erebusnz/tachyon/gerber/audit-backing-board.md

# PCB Audit — backing-board

**Auto-generated by `.claude/skills/pcb-designer/scripts/run_audit.py`**

## Sources

- Telesis netlist: indexed (31 package types, 59 nets)
- Pick-and-place: 74 components
- Gerber: gerber\audio-mcu-board (16 layers)

## Findings

- Layout errors (need EasyEDA Pro fix): **0**
- Stale documentation (need MD edit): **0**
- Advisories: **0**

## Observations

- Stackup: 4-layer (15 gerber layers). G1 (regions=251, copper_areas=0). G2 (regions=6, copper_areas=6).
- .G1: single GND pour ✓ (regions=251, copper_areas=0). Confirm electrical continuity visually if encoded as many SolidRegions.
- .G2: 6 PlaneZones — power layer split per pcb-design.md §4 ✓ (matches expected rail count)
- Board outline: 48.00 × 110.00 mm (X[0.00,48.00] Y[-110.00,0.00])
- Named nets: ['+12V', '+3V3', '+3V3_AUDIO', '+3V3_PREC', '+5V', '-12V', '-12VEURO', '12VEURO', 'A-OUT-L', 'A-OUT-R', 'CLK-IN', 'CV-IN-A', 'CV-IN-B', 'CV-OUT-A', 'CV-OUT-B', 'DAC-SPI-CS', 'DAC-SPI-MOSI', 'DAC-SPI-SCLK', 'GATE-OUT-A', 'GATE-OUT-B', 'GND', 'I2S3_BCK', 'I2S3_SD', 'I2S3_WS', 'U12-BOOT', 'U12-FB', 'U12-SW', 'USR-ENC-A', 'USR-ENC-B', 'USR-ENC-SW', 'USR-POT-1', 'VREF', '~MUTE']
- Anonymous (auto-generated $...) nets: 21
- Single ground net (GND): ✓ matches pcb-design.md §3.
- Datasheet power/ground pin connectivity: 17 power/GND pin(s) across 5 IC(s) all connected ✓ (would flag a floating supply/GND pin, e.g. the U6 pin-8 GND case).
- Eurorack 10-pin header P1: standard pinout ✓ ({-12V:[1, 2], GND:[3, 4, 5, 6, 7, 8], +12V:[9, 10]}). Verify silk stripe sits on -12V edge in EasyEDA Pro 2D view.
- Pass 3: skipping U1 (sub-module with internal decoupling).
- Decoupling U12 +12V: nearest cap C5 at 3.05 mm ✓
- Decoupling U14 +3V3_PREC: nearest cap C11 at 3.79 mm ✓
- Decoupling U14 +5V: nearest cap C9 at 4.75 mm ✓
- Decoupling U15 +3V3_AUDIO: nearest cap C14 at 3.84 mm ✓
- Decoupling U15 +5V: nearest cap C12 at 5.04 mm ✓
- Decoupling U16 +12V: nearest cap C36 at 6.04 mm ✓
- Decoupling U16 -12V: nearest cap C35 at 5.23 mm ✓
- Decoupling U2 +3V3_PREC: nearest cap C15 at 5.39 mm ✓
- Decoupling U3 +3V3: nearest cap C26 at 6.65 mm ✓
- Decoupling U3 +3V3_AUDIO: nearest cap C31 at 5.80 mm ✓
- Decoupling U6 +3V3_PREC: nearest cap C18 at 5.38 mm ✓
- Decoupling U7 +12V: nearest cap C22 at 5.49 mm ✓
- Decoupling U7 -12V: nearest cap C23 at 5.43 mm ✓
- Spacing U12↔U3 = 50.40 mm (ge 30.0 mm): ✓ — TPS54202 (noisy buck) ↔ PCM5102A (audio DAC) — pcb-design.md §5
- Spacing U12↔U2 = 44.30 mm (ge 30.0 mm): ✓ — TPS54202 (noisy buck) ↔ REF5025 (precision ref) — pcb-design.md §5
- Spacing U12↔U16 = 33.53 mm (ge 30.0 mm): ✓ — TPS54202 (noisy buck) ↔ OPA1642 audio buffers — analogous to U3
- Spacing U2↔U6 = 11.65 mm (le 20.0 mm): ✓ — REF5025 ↔ DAC8552 — cv-output-dac.md §6 (VREF trace)
- Placement U12  at (   7.6,    -5.6) side=top    fp=SOT-23-6_L2.9-W1.6-P0.95-LS2.8-BL
- Placement P1   at (  41.9,   -11.6) side=bottom fp=IDC-TH_10P-P2.54_C5665
- Placement U14  at (  28.8,   -31.0) side=top    fp=SOT-23-5_L2.9-W1.6-P0.95-LS2.8-BR
- Placement U15  at (  17.5,   -30.9) side=top    fp=SOT-23-5_L2.9-W1.6-P0.95-LS2.8-BR
- Placement U16  at (   8.1,   -39.1) side=top    fp=SOIC-8_L4.9-W3.9-P1.27-LS6.0-BL
- Placement U2   at (  27.9,   -45.0) side=top    fp=SOIC-8_L4.9-W3.9-P1.27-LS6.0-BL-4
- Placement U7   at (  37.6,   -44.2) side=top    fp=SOIC-8_L4.9-W3.9-P1.27-LS6.0-BL
- Placement U6   at (  31.2,   -56.1) side=top    fp=VSSOP-8_L3.0-W3.0-P0.65-LS5.0-BL
- Placement U3   at (  15.5,   -55.4) side=top    fp=TSSOP-20_L6.5-W4.4-P0.65-LS6.4-BL
- Placement U1   at (  24.5,   -81.8) side=bottom fp=WeAct STM32F405RGT6
- Placement H2   at (   3.0,   -39.6) side=top    fp=HDR-TH_4P-P2.54-V-M-1
- Placement H3   at (  45.0,   -32.3) side=top    fp=HDR-TH_8P-P2.54-V-M
- Placement H4   at (   3.0,   -72.6) side=top    fp=HDR-TH_8P-P2.54-V-M
- Placement H9   at (  45.0,   -77.7) side=top    fp=HDR-TH_12P-P2.54-V-M
- I2S3_BCK: members ['U1', 'U3']
- I2S3_SD: members ['U1', 'U3']
- I2S3_WS: members ['U1', 'U3']
- Trace widths on .GBL: 0.203mm×476, 0.254mm×63, 0.500mm×11, 1.000mm×13
- Trace widths on .G2: 0.203mm×670
- Trace widths on .GTL: 0.203mm×1349, 0.254mm×281, 0.400mm×9, 0.500mm×41, 0.700mm×4, 0.750mm×1, 0.800mm×2, 1.000mm×32
- Per-net trace-width compliance (e.g. '+5V must be ≥ 0.6 mm') cannot be verified from gerber geometry alone — the gerber encodes geometry without net assignment. Verify visually in the EasyEDA Pro 2D view or by exporting routed length per net from the project.
