erebusnz/tachyon/gerber/audit-front-board.md

# PCB Audit — front-board

**Auto-generated by `.claude/skills/pcb-designer/scripts/run_audit.py`**

## Sources

- Telesis netlist: indexed (0 package types, 0 nets)
- Pick-and-place: 8 components
- Gerber: gerber\front-board (9 layers)

## Findings

- Layout errors (need EasyEDA Pro fix): **0**
- Stale documentation (need MD edit): **0**
- Advisories: **0**

## Observations

- Stackup: 2-layer (9 gerber layers, no .G1/.G2)
- Board outline: 50.50 × 128.50 mm (X[-26.05,24.45] Y[-64.16,64.34])

## Skipped passes

- Passes 2-6: no electrical content (empty netlist)
