erebusnz/tachyon/gerber/audit-io-board.md

# PCB Audit — io-board

**Auto-generated by `.claude/skills/pcb-designer/scripts/run_audit.py`**

## Sources

- Telesis netlist: indexed (15 package types, 37 nets)
- Pick-and-place: 44 components
- Gerber: gerber\io-board (16 layers)

## Findings

- Layout errors (need EasyEDA Pro fix): **0**
- Stale documentation (need MD edit): **0**
- Advisories: **0**

## Observations

- Stackup: 4-layer (15 gerber layers). G1 (regions=212, copper_areas=0). G2 (regions=212, copper_areas=0).
- .G1: single GND pour ✓ (regions=212, copper_areas=0). Confirm electrical continuity visually if encoded as many SolidRegions.
- .G2: single GND pour ✓ (regions=212, copper_areas=0). Confirm electrical continuity visually if encoded as many SolidRegions.
- Board outline: 49.27 × 119.53 mm (X[0.00,49.27] Y[-119.53,0.00])
- Named nets: ['+12V', '+3V3', '+5V', '-12V', 'A-OUT-L', 'A-OUT-R', 'CLK-IN', 'CV-IN-A', 'CV-IN-B', 'CV-OUT-A', 'CV-OUT-B', 'GATE-OUT-A', 'GATE-OUT-B', 'GND', 'USR-ENC-A', 'USR-ENC-B', 'USR-ENC-SW', 'USR-POT-1', 'VREF']
- Anonymous (auto-generated $...) nets: 18
- Single ground net (GND): ✓ matches pcb-design.md §3.
- Decoupling U23 +12V: nearest cap C40 at 5.23 mm ✓
- Decoupling U23 -12V: nearest cap C41 at 5.57 mm ✓
- Pass 4: no spacing rules defined for io-board in SPACING_RULES.
- Trace widths on .GBL: 0.203mm×712, 0.254mm×234, 0.500mm×9
- Trace widths on .GTL: 0.203mm×789, 0.254mm×247
- Per-net trace-width compliance (e.g. '+5V must be ≥ 0.6 mm') cannot be verified from gerber geometry alone — the gerber encodes geometry without net assignment. Verify visually in the EasyEDA Pro 2D view or by exporting routed length per net from the project.

## Skipped passes

- Pass 5 (I2S): no I2S on this board.
