erebusnz/tachyon/datasheets/REF5025.md

# REF5025 -- Low-Noise, Very Low Drift, 2.5V Precision Voltage Reference

## BOM Details

| Field | Value |
|---|---|
| MPN | REF5025IDR |
| Manufacturer | TI |
| Package | SOIC-8_L4.9-W3.9-P1.27-LS6.0-BL-4 |
| Designator | U2 |
| Quantity | 1 |
| Supplier Part  | C544535 (LCSC) |

## Description

The REF5025 is a low-noise, low-drift, precision 2.5V voltage reference from the REF50xx family by Texas Instruments. The standard-grade REF5025IDR (I-suffix) provides 0.1% initial accuracy (max) and 8 ppm/degC temperature drift (max). The higher-grade REF5025AIDR (AI-suffix) tightens these to 0.05% and 3 ppm/degC. It is capable of sourcing and sinking up to 10 mA of output current, making it suitable for driving ADC and DAC reference inputs.

## Key Electrical Characteristics

All values at TA = 25 degC, ILOAD = 0, CL = 1 uF, VIN = (VOUT + 0.2V) to 18V unless otherwise noted. REF5025IDR is the standard-grade (I-suffix) device.

| Parameter | Min | Typ | Max | Unit | Condition |
|---|---|---|---|---|---|
| Output voltage | 2.4975 | 2.5000 | 2.5025 | V | TA = 25 degC, derived from ±0.1 % accuracy |
| Initial accuracy (standard grade) | -0.1 | | +0.1 | % | All voltage options, TA = 25 degC |
| Temperature drift (standard grade) | | 3 | 8 | ppm/degC| TA = -40 degC to +125 degC |
| Low-frequency noise | | 3 | | uVpp/V  | f = 0.1 Hz to 10 Hz (= 7.5 uVpp at 2.5 V) |
| Output voltage noise | | 0.9 | | uVrms/V | f = 10 Hz to 1 kHz, integrated |
| Line regulation | | 1 | 3 | ppm/V | VIN = (VOUT + 0.2V) to 18V |
| Line regulation (over temperature) | | 1 | 5 | ppm/V | VIN = (VOUT + 0.2V) to 18V, -40 to +125 degC |
| Load regulation | | 20 | 30 | ppm/mA  | -10 mA < IOUT < 10 mA, VIN = VOUT + 0.75V |
| Load regulation (over temperature) | | | 50 | ppm/mA  | -10 mA < IOUT < 10 mA, -40 to +125 degC |
| Short-circuit current | | 25 | | mA | VOUT shorted to GND |
| Output current (source/sink) | -10 | | +10 | mA | |
| Turn-on settling time | | 200 | | us | To 0.1 % with CL = 1 uF |
| Supply voltage (Vs) | 2.7 | | 18 | V | REF5025: min is 2.7 V (footnote: VOUT ≤ 2.5 V) |
| Quiescent current | | 0.8 | 1.0 | mA | TA = 25 degC, no load |
| Quiescent current (over temperature) | | | 1.2 | mA | TA = -40 degC to +125 degC |
| Specified temperature range | -40 | | +125 | degC | |
| Operating temperature range | -55 | | +125 | degC | |
| Long-term drift (SOIC-8) | | 22 | | ppm | 0 to 1000 hours |
| Long-term drift (SOIC-8) | | 18 | | ppm | 1000 to 2000 hours |
| Thermal hysteresis (SOIC-8 std grade)  | | 90 | | ppm | Cycle 1, -40 degC to +125 degC |
| Thermal hysteresis (SOIC-8 std grade)  | | 50 | | ppm | Cycle 2, -40 degC to +125 degC |
| TEMP pin output | | 575 | | mV | TA = 25 degC |
| TEMP pin sensitivity | | 2.64 | | mV/degC | TA = -40 degC to +125 degC |

## Pinout

SOIC-8 (D package) only.

| Pin # | Name | Direction | Description |
|---|---|---|---|
| 1 | DNC | -- | Do not connect |
| 2 | VIN | P | Power supply input (2.7V to 18V for REF5025) |
| 3 | TEMP | O | Temperature sensor output (analog) |
| 4 | GND | G | Ground |
| 5 | TRIM/NR| I | Noise reduction / output trim pin |
| 6 | VOUT | O | Regulated 2.5V reference output |
| 7 | NC | NC | No internal connection |
| 8 | DNC | -- | Do not connect |

Direction key: I = Input, O = Output, P = Power, G = Ground, NC = No Connect, DNC = Do Not Connect

## Absolute Maximum Ratings

| Parameter | Min | Max | Unit  |
|---|---|---|---|
| Input voltage (VIN) | -0.2  | 18 | V |
| Output short-circuit current | -30 | +30 | mA |
| Operating temperature range | -55 | +125  | degC  |
| Junction temperature (TJ max) | | +150  | degC  |
| Storage temperature range | -65 | +150  | degC  |
| ESD (HBM, ANSI/ESDA/JEDEC JS-001) | -3000 | +3000 | V |
| ESD (CDM, JESD22-C101) | -1000 | +1000 | V |

## Application Notes

- **Decoupling**: Place a 0.1 uF ceramic capacitor close to the VIN pin (pin 2). A 1 uF to 10 uF ceramic or tantalum capacitor is recommended on VOUT (pin 6) for stability and transient response. The output is stable with any capacitive load.
- **Noise reduction pin (TRIM/NR)**: Connect an external capacitor (typically 0.1 uF to 1 uF) from pin 5 (TRIM/NR) to GND to reduce broadband output noise. Larger capacitors yield lower noise but slower startup.
- **DNC pins**: Pins 1 and 8 are Do-Not-Connect. Leave them floating; do not tie to any net (this package variant has no EN pin).
- **Minimum input headroom**: VS must be at least VOUT + 0.2 V; for the REF5025 specifically the datasheet floor is **2.7 V** (footnote (1) on §6.5 Power Supply row).
- **Load current**: The output can source up to +10 mA and sink up to -10 mA. Exceeding these limits degrades accuracy and may damage the device.
- **Thermal considerations**: The integrated temperature sensor on pin 3 outputs a voltage proportional to die temperature (~2 mV/degC) and can be used for system-level thermal compensation.
- **Long-term stability**: The SOIC-8 package provides better long-term drift (22 ppm/1000 hrs) compared to the VSSOP-8 package (50 ppm/1000 hrs).
