erebusnz/tachyon/datasheets/PCM5102A.md

# PCM5102A -- 2.1 VRMS DirectPath 112 dB Stereo Audio DAC

## BOM Details

| Field | Value |
|---|---|
| MPN | PCM5102APWR |
| Manufacturer | TI |
| Package/Footprint | TSSOP-20_L6.5-W4.4-P0.65-LS6.4-BL |
| Designator | U3 |
| Quantity | 1 |
| Supplier Part | C107671 (LCSC) |

## Description

The PCM5102A is a 32-bit, 384 kHz stereo audio DAC from Texas Instruments featuring an integrated line-level output driver with DirectPath technology, which provides a ground-centered output that eliminates the need for DC-blocking capacitors. It includes a high-performance audio PLL that generates the system clock internally from the BCK reference, removing the requirement for an external master clock (SCK). The device accepts I2S or left-justified audio data in 16-, 24-, or 32-bit formats and is configured entirely via hardware pins.

## Key Electrical Characteristics

| Parameter | Min | Typ | Max | Unit | Condition |
|---|---|---|---|---|---|
| Resolution | -- | 32 | -- | bits | -- |
| Signal-to-Noise Ratio (SNR) | -- | 112 | -- | dB | A-weighted, 1 kHz |
| Dynamic Range | -- | 112 | -- | dB | A-weighted, 1 kHz, -60 dBFS |
| THD+N | -- | -93 | -- | dB | 1 kHz, 0 dBFS |
| Output Voltage (VOUT) | -- | 2.1 | -- | VRMS | Full-scale, 1 kHz |
| Channel Separation | -- | 100 | -- | dB | 1 kHz |
| Sample Rate (fS) | 8 | -- | 384 | kHz | -- |
| Analog Supply Voltage (AVDD) | 3.0 | 3.3 | 3.6 | V | -- |
| Digital Supply Voltage (DVDD) | 1.65 | 3.3 | 3.6 | V | 1.8 V or 3.3 V nominal |
| Charge Pump Supply (CPVDD) | 3.0 | 3.3 | 3.6 | V | -- |
| Analog Supply Current (AVDD) | -- | 17 | -- | mA | Normal operation |
| Digital Supply Current (DVDD) | -- | 3 | -- | mA | Normal operation at 3.3 V |
| Charge Pump Supply Current (CPVDD) | -- | 4.5 | -- | mA | Normal operation |
| Power-Down Current | -- | -- | 0.1 | uA | XSMT = LOW |
| Output Load Resistance | 1 | -- | -- | kohm | Minimum load |
| I2S Data Format | -- | -- | -- | -- | I2S (FMT = LOW) or left-justified (FMT = HIGH) |
| BCK-to-LRCK Ratio | 32 | -- | 128 | -- | BCK/LRCK per channel |

## Pinout

TSSOP-20 (PW) package only.

| Pin # | Name | Direction | Description |
|---|---|---|---|
| 1 | CPVDD | P | Charge pump power supply (3.3 V) |
| 2 | CAPP | P | Charge pump flying capacitor positive terminal |
| 3 | CPGND | G | Charge pump ground |
| 4 | CAPM | P | Charge pump flying capacitor negative terminal |
| 5 | VNEG | O | Charge pump negative voltage output (decouple to CPGND) |
| 6 | OUTL | O | Left-channel analog audio output |
| 7 | OUTR | O | Right-channel analog audio output |
| 8 | AVDD | P | Analog power supply (3.3 V) |
| 9 | AGND | G | Analog ground for DAC and output stage |
| 10 | DEMP | I | De-emphasis control: LOW = disabled, HIGH = 44.1 kHz de-emphasis enabled |
| 11 | FLT | I | Digital filter select: LOW = normal latency, HIGH = low latency |
| 12 | SCK | I | System clock input (connect to GND to use internal PLL from BCK) |
| 13 | BCK | I | Audio bit clock input |
| 14 | DIN | I | Audio serial data input (I2S or left-justified) |
| 15 | LRCK | I | Audio left/right word clock input |
| 16 | FMT | I | Audio format select: LOW = I2S, HIGH = left-justified |
| 17 | XSMT | I | Soft mute control: LOW = soft mute (output muted), HIGH = normal operation |
| 18 | LDOO | P | Internal 1.8 V LDO regulator output (decouple with 1 uF to DGND) |
| 19 | DGND | G | Digital ground |
| 20 | DVDD | P | Digital power supply (1.8 V or 3.3 V) |

Direction key: I = Input, O = Output, P = Power, G = Ground.

## Absolute Maximum Ratings

| Parameter | Min | Max | Unit |
|---|---|---|---|
| AVDD to AGND | -0.3 | +3.9 | V |
| DVDD to DGND | -0.3 | +3.9 | V |
| CPVDD to CPGND | -0.3 | +3.9 | V |
| Digital Input Voltage (BCK, DIN, LRCK, SCK, FMT, FLT, DEMP, XSMT) | -0.3 | DVDD + 0.3 | V |
| Analog Output Current (OUTL, OUTR) | -- | +/- 20 | mA |
| Operating Temperature | -25 | +85 | deg C |
| Storage Temperature | -65 | +150 | deg C |
| Junction Temperature | -- | +150 | deg C |
| ESD (HBM) | -- | 2000 | V |
| ESD (CDM) | -- | 500 | V |

Stresses beyond those listed may cause permanent damage. Exposure to absolute maximum conditions for extended periods may affect device reliability.

## Application Notes

- **I2S interface:** The PCM5102A accepts standard I2S or left-justified PCM audio data via three signals: BCK (bit clock), DIN (serial data), and LRCK (left/right word clock). No master clock (SCK) is required when using the internal PLL -- connect SCK directly to GND. The internal PLL locks to BCK and generates all required internal clocks. Supported BCK-to-LRCK ratios are 32, 48, and 64 per channel (i.e., 64, 96, or 128 BCK cycles per LRCK frame). The device accepts 16-, 24-, and 32-bit audio words.
- **Audio format config pins:** FMT selects between I2S format (LOW) and left-justified format (HIGH). FLT selects the digital interpolation filter: normal latency (LOW) provides a sharp roll-off filter, while low latency (HIGH) provides a slow roll-off filter with reduced group delay. DEMP enables 44.1 kHz digital de-emphasis when HIGH. XSMT controls the soft mute function: drive HIGH for normal operation, LOW to engage a soft mute ramp that achieves 120 dB of mute attenuation. On power-up, XSMT should be held LOW until clocks are stable, then driven HIGH to unmute.
- **Power supply:** The device requires three supply rails: AVDD (3.3 V analog), DVDD (1.8 V or 3.3 V digital), and CPVDD (3.3 V charge pump). When DVDD is supplied at 3.3 V, the internal LDO regulates it down to 1.8 V for the digital core -- the LDO output (LDOO, pin 18) must be decoupled with a 1 uF ceramic capacitor. AVDD and CPVDD should share the same 3.3 V supply but be decoupled independently.
- **Decoupling:** Place 10 uF + 100 nF ceramic capacitors on AVDD (pin 8) and CPVDD (pin 1), each as close to the pin as possible. Place a 1 uF ceramic capacitor on LDOO (pin 18). Place a 100 nF ceramic capacitor on DVDD (pin 20). Decouple VNEG (pin 5) with a 1 uF ceramic capacitor to CPGND.
- **Charge pump capacitors:** Connect a 220 nF to 1 uF ceramic capacitor between CAPP (pin 2) and CAPM (pin 4). This flying capacitor is used by the internal charge pump to generate the negative supply rail (VNEG) for the ground-centered output stage.
- **Output stage:** The DirectPath output eliminates the need for external DC-blocking capacitors. OUTL and OUTR provide a ground-centered 2.1 VRMS full-scale signal that can drive loads down to 1 kohm directly. For best performance, keep the output traces short and route them away from digital signals. A series resistor (e.g., 470 ohm) can be used to form a low-pass filter with the cable capacitance for EMI filtering.
- **Grounding:** Maintain separate analog ground (AGND) and digital ground planes. Connect AGND (pin 9), CPGND (pin 3), and DGND (pin 19) together at a single star point near the device.
