erebusnz/tachyon/firmware/Drivers/WAVESHARE_OLED/OLED/OLED_1in5.c

/*****************************************************************************
* | File      	:   OLED_1in5.c
* | Author      :   Waveshare team
* | Function    :   1.5inch OLED Module Drive function
* | Info        :
*----------------
* |	This version:   V2.0
* | Date        :   2020-08-15
* | Info        :
* -----------------------------------------------------------------------------
#
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
******************************************************************************/
#include "OLED_1in5.h"
#include "stdio.h"

/*******************************************************************************
function:
            Hardware reset
*******************************************************************************/
static void OLED_Reset(void)
{
    OLED_RST_1;
    Driver_Delay_ms(100);
    OLED_RST_0;
    Driver_Delay_ms(100);
    OLED_RST_1;
    Driver_Delay_ms(100);
}

/*******************************************************************************
function:
            Write register address and data
*******************************************************************************/
static void OLED_WriteReg(uint8_t Reg)
{
#if USE_SPI_4W
	OLED_DC_0;
    OLED_CS_0;
    SPI4W_Write_Byte(Reg);
    OLED_CS_1;
#elif USE_IIC
    I2C_Write_Byte(Reg,IIC_CMD);
#endif
}

static void OLED_WriteData(uint8_t Data)
{   
#if USE_SPI_4W
    OLED_DC_1;
    OLED_CS_0;
    SPI4W_Write_Byte(Data);
    OLED_CS_1;
#elif USE_IIC
    I2C_Write_Byte(Data,IIC_RAM);
#endif
}

/*******************************************************************************
function:
        Common register initialization
*******************************************************************************/
static void OLED_InitReg(void)
{
    OLED_WriteReg(0xae);//--turn off oled panel

    OLED_WriteReg(0x15);    //   set column address
    OLED_WriteReg(0x00);    //  start column   0
    OLED_WriteReg(0x7f);    //  end column   127

    OLED_WriteReg(0x75);    //   set row address
    OLED_WriteReg(0x00);    //  start row   0
    OLED_WriteReg(0x7f);    //  end row   127

    OLED_WriteReg(0x81);  // set contrast control
    OLED_WriteReg(0x80);

    OLED_WriteReg(0xa0);    // gment remap
    OLED_WriteReg(0x51);   //51

    OLED_WriteReg(0xa1);  // start line
    OLED_WriteReg(0x00);

    OLED_WriteReg(0xa2);  // display offset
    OLED_WriteReg(0x00);

    OLED_WriteReg(0xa4);    // rmal display
    OLED_WriteReg(0xa8);    // set multiplex ratio
    OLED_WriteReg(0x7f);

    OLED_WriteReg(0xb1);  // set phase leghth
    OLED_WriteReg(0xf1);

    OLED_WriteReg(0xb3);  // set dclk
    OLED_WriteReg(0x00);  //80Hz:0xc1 90Hz:0xe1   100Hz:0x00   110Hz:0x30 120Hz:0x50   130Hz:0x70     01

    OLED_WriteReg(0xab);  //
    OLED_WriteReg(0x01);  //

    OLED_WriteReg(0xb6);  // set phase leghth
    OLED_WriteReg(0x0f);

    OLED_WriteReg(0xbe);
    OLED_WriteReg(0x0f);

    OLED_WriteReg(0xbc);
    OLED_WriteReg(0x08);

    OLED_WriteReg(0xd5);
    OLED_WriteReg(0x62);

    OLED_WriteReg(0xfd);
    OLED_WriteReg(0x12);

}

/********************************************************************************
function:
            initialization
********************************************************************************/
void OLED_1in5_Init(void)
{
    //Hardware reset
    OLED_Reset();

    //Set the initialization register
    OLED_InitReg();
    Driver_Delay_ms(200);

    //Turn on the OLED display
    OLED_WriteReg(0xAF);
}

/********************************************************************************
function:   Set the display Window(Xstart, Ystart, Xend, Yend)
parameter:
        xStart :   X direction Start coordinates
        Ystart :   Y direction Start coordinates
        Xend   :   X direction end coordinates
        Yend   :   Y direction end coordinates
********************************************************************************/
static void OLED_SetWindow(UBYTE Xstart, UBYTE Ystart, UBYTE Xend, UBYTE Yend)
{
    if((Xstart > OLED_1in5_WIDTH) || (Ystart > OLED_1in5_HEIGHT) ||
       (Xend > OLED_1in5_WIDTH) || (Yend > OLED_1in5_HEIGHT))
        return;

    OLED_WriteReg(0x15);
    OLED_WriteReg(Xstart/2);
    OLED_WriteReg(Xend/2 - 1);

    OLED_WriteReg(0x75);
    OLED_WriteReg(Ystart);
    OLED_WriteReg(Yend - 1);
}

/********************************************************************************
function:
            Clear screen
********************************************************************************/
void OLED_1in5_Clear(void)
{
    UWORD i;
    OLED_SetWindow(0, 0, 128, 128);
    for(i=0; i<OLED_1in5_WIDTH*OLED_1in5_HEIGHT/2; i++){
        OLED_WriteData(0x00);
    }
}

/********************************************************************************
function:   Update all memory to OLED
********************************************************************************/
void OLED_1in5_Display(const UBYTE *Image)
{
#if USE_SPI_4W
    /* Whole frame in one DMA transfer: DC high + CS low once, then 8 KB pushed
     * by DMA2 while the caller keeps running (CS is released from the transfer
     * IRQ). Returns immediately; the caller must not redraw `Image` until the
     * next call (which waits for the previous blit to finish). The old per-byte
     * path took tens of ms per frame and dominated the main-loop period. */
    SPI4W_Wait_Idle();               /* previous frame + keep reg writes clear */
    OLED_SetWindow(0, 0, 128, 128);
    OLED_DC_1;
    OLED_CS_0;
    if (SPI4W_Write_DMA(Image, OLED_1in5_WIDTH / 2 * OLED_1in5_HEIGHT) != 0) {
        /* DMA rejected (shouldn't happen) — blocking fallback. */
        SPI4W_Write_nByte(Image, OLED_1in5_WIDTH / 2 * OLED_1in5_HEIGHT);
        OLED_CS_1;
    }
#else
    UWORD i, j;
    OLED_SetWindow(0, 0, 128, 128);
    for(i=0; i<OLED_1in5_HEIGHT; i++)
        for(j=0; j<OLED_1in5_WIDTH/2; j++)
        {
            OLED_WriteData(Image[j + i*64]);
        }
#endif
}
