erebusnz/tachyon/firmware/Core/UI/circle_of_fifths.c

#include "circle_of_fifths.h"
#include "GUI_Paint.h"
#include "note_sprites.h"
#include <math.h>

#define WIDTH          128
#define HEIGHT         128
#define NUM_SEGMENTS   12
#define SEGMENT_ANGLE  30.0f   // 360 / 12
#define NUM_VISIBLE    2

#define OUTER_RADIUS   400.0f
#define INNER_RADIUS   (OUTER_RADIUS * 0.75f)
#define BORDER_WIDTH   5.0f

#define GREY_LIGHT     13
#define GREY_DARK      2
#define BG_LEVEL       0
#define BORDER_LEVEL   15
#define MARK_INSET     6.0f   /* virtual units of black ring inside marked segment */

#define DEG2RAD        (3.14159265f / 180.0f)
#define RAD2DEG        (180.0f / 3.14159265f)

// Number of accidentals per note (C=0, G=1, ... F#=6, ... F=1)
static const uint8_t accidentals[NUM_SEGMENTS] = {
    0, 1, 2, 3, 4, 5, 6, 5, 4, 3, 2, 1
};

// Sprite angle indices: 0=-30°, 1=0°, 2=+30°
static const float sprite_angles[NOTE_SPRITE_NUM_ANGLES] = {
    -30.0f, 0.0f, 30.0f
};

// Viewport (constant, computed once)
static float vp_x, vp_y, vp_size;
static int vp_ready = 0;

static void compute_viewport(void)
{
    float half_span = NUM_VISIBLE * SEGMENT_ANGLE / 2.0f;
    float ang_start = -90.0f - half_span;
    float ang_end   = -90.0f + half_span;

    float min_x = 1e9f, min_y = 1e9f;
    float max_x = -1e9f, max_y = -1e9f;

    int steps = 64;
    for (int s = 0; s <= steps; s++) {
        float ang = (ang_start + (ang_end - ang_start) * s / steps) * DEG2RAD;
        float ca = cosf(ang);
        float sa = sinf(ang);
        for (int ri = 0; ri < 2; ri++) {
            float r = (ri == 0) ? INNER_RADIUS : OUTER_RADIUS;
            float x = r * ca;
            float y = r * sa;
            if (x < min_x) min_x = x;
            if (x > max_x) max_x = x;
            if (y < min_y) min_y = y;
            if (y > max_y) max_y = y;
        }
    }

    float padding = BORDER_WIDTH + 2.0f;
    min_x -= padding;  min_y -= padding;
    max_x += padding;  max_y += padding;

    float w = max_x - min_x;
    float h = max_y - min_y;
    float size = (w > h) ? w : h;
    float mid_x = (min_x + max_x) / 2.0f;
    float mid_y = (min_y + max_y) / 2.0f;

    size *= 1.05f;
    vp_x = mid_x - size / 2.0f;
    vp_y = mid_y - size / 2.0f;
    vp_size = size;
    vp_ready = 1;
}

// Find nearest sprite angle index
static int angle_index(float theta_from_top)
{
    int best = 0;
    float best_dist = fabsf(theta_from_top - sprite_angles[0]);
    for (int i = 1; i < NOTE_SPRITE_NUM_ANGLES; i++) {
        float d = fabsf(theta_from_top - sprite_angles[i]);
        if (d < best_dist) { best_dist = d; best = i; }
    }
    return best;
}

// Get a 4-bit pixel from packed sprite data (high nibble first)
static inline uint8_t sprite_get(const uint8_t *buf, int x, int y, int w)
{
    int idx = y * w + x;
    int byte = idx / 2;
    if (idx & 1)
        return buf[byte] & 0x0F;
    else
        return (buf[byte] >> 4) & 0x0F;
}

/* ---- geometry LUT ----------------------------------------------------------
 *
 * Rendering ray-traces the donut per pixel (sqrtf + atan2f x 16k pixels ≈
 * 35 ms) — but rotation is snapped to 30° detents, and a snapped rotation
 * only PERMUTES which segment index lands on each pixel; the geometry
 * (border/mark-ring distances, anti-aliasing) never changes. So the float
 * math runs once into a 2-byte-per-pixel LUT and each frame is integer
 * blends (~1 ms).
 *
 * byte0 high nibble: segment index at rotation 0 (0..11),
 *                    LUT_OUTSIDE = background fill near the ring's AA fringe,
 *                    LUT_SKIP    = pure background (pixel untouched).
 * byte0 low nibble:  mark-ring alpha x 15 (inset black ring, marked segments).
 * byte1:             border alpha x 255 (blend fill -> BORDER_LEVEL).
 *
 * 32 KB, in CCM-RAM next to the PCM pool (CPU-only, no DMA access). */
#define LUT_OUTSIDE  0xE
#define LUT_SKIP     0xF

__attribute__((section(".ccmbss")))
static uint8_t s_lut[WIDTH * HEIGHT * 2];
static int s_lut_ready = 0;

static uint8_t seg_grey_lut(int seg)
{
    float t = accidentals[seg] / 6.0f;
    return (uint8_t)(GREY_LIGHT + t * (GREY_DARK - GREY_LIGHT) + 0.5f);
}

static void build_lut(void)
{
    if (!vp_ready)
        compute_viewport();

    float half_bw = BORDER_WIDTH / 2.0f;
    uint8_t *out = s_lut;

    for (int py = 0; py < HEIGHT; py++) {
        for (int px = 0; px < WIDTH; px++) {
            float x = vp_x + (px + 0.5f) / WIDTH * vp_size;
            float y = vp_y + (py + 0.5f) / HEIGHT * vp_size;

            float r = sqrtf(x * x + y * y);

            float dist_outer = r - OUTER_RADIUS;
            float dist_inner = INNER_RADIUS - r;

            if (dist_outer > half_bw + 1.0f || dist_inner > half_bw + 1.0f) {
                *out++ = LUT_SKIP << 4;
                *out++ = 0;
                continue;
            }

            float angle = atan2f(y, x) * RAD2DEG;
            float adjusted = fmodf(angle + 90.0f + SEGMENT_ANGLE / 2.0f + 720.0f, 360.0f);
            int seg_index = (int)(adjusted / SEGMENT_ANGLE);
            if (seg_index >= NUM_SEGMENTS) seg_index = 0;
            float seg_pos = adjusted - seg_index * SEGMENT_ANGLE;

            float dist_to_start = seg_pos * DEG2RAD * r;
            float dist_to_end = (SEGMENT_ANGLE - seg_pos) * DEG2RAD * r;
            float dist_radial = (dist_to_start < dist_to_end) ? dist_to_start : dist_to_end;

            float dist_circle = fabsf(dist_outer);
            float d = fabsf(dist_inner);
            if (d < dist_circle) dist_circle = d;
            float dist_border = (dist_circle < dist_radial) ? dist_circle : dist_radial;

            float border_alpha = (dist_border - half_bw + 1.0f) / 2.0f;
            if (border_alpha < 0.0f) border_alpha = 0.0f;
            if (border_alpha > 1.0f) border_alpha = 1.0f;

            uint8_t hi, mark_q;
            if (dist_outer > 0.0f || dist_inner > 0.0f) {
                hi = LUT_OUTSIDE;
                mark_q = 0;
            } else {
                hi = (uint8_t)seg_index;
                /* Inset black ring alpha for marked segments: just inside the
                 * white border. */
                float a = (half_bw + MARK_INSET) - dist_border;
                if (a < 0.0f) a = 0.0f;
                if (a > 1.0f) a = 1.0f;
                mark_q = (uint8_t)(a * 15.0f + 0.5f);
            }

            *out++ = (uint8_t)((hi << 4) | mark_q);
            *out++ = (uint8_t)(border_alpha * 255.0f + 0.5f);
        }
    }

    s_lut_ready = 1;
}

void cof_prewarm(void)
{
    if (!s_lut_ready)
        build_lut();
}

void cof_render_angle(float angle_deg, const uint8_t *marked)
{
    if (!s_lut_ready)
        build_lut();

    // Snap to 30° detent positions.
    float snapped = roundf(angle_deg / 30.0f) * 30.0f;
    float rotation = -snapped;
    /* Snapped rotation shifts every pixel's segment index by whole segments. */
    int rot_steps = (((int)lroundf(snapped / SEGMENT_ANGLE)) % NUM_SEGMENTS
                     + NUM_SEGMENTS) % NUM_SEGMENTS;

    // Precompute segment grey levels
    uint8_t seg_grey[NUM_SEGMENTS];
    for (int i = 0; i < NUM_SEGMENTS; i++)
        seg_grey[i] = seg_grey_lut(i);

    Paint_Clear(BG_LEVEL);

    // --- Pass 1: donut segments from the LUT ---
    const uint8_t *lut = s_lut;
    for (int py = 0; py < HEIGHT; py++) {
        for (int px = 0; px < WIDTH; px++) {
            uint8_t b0 = *lut++;
            uint8_t a8 = *lut++;
            uint8_t hi = b0 >> 4;
            if (hi == LUT_SKIP) continue;

            int fill;
            if (hi == LUT_OUTSIDE) {
                fill = BG_LEVEL;
            } else {
                int seg = hi + rot_steps;
                if (seg >= NUM_SEGMENTS) seg -= NUM_SEGMENTS;
                fill = seg_grey[seg];
                if (marked && marked[seg]) {
                    int m = b0 & 0x0F;                    /* mark alpha x 15 */
                    fill = (fill * (15 - m) + 7) / 15;    /* blend -> BG (0) */
                }
            }

            int pixel = (fill * a8 + BORDER_LEVEL * (255 - a8) + 127) / 255;
            if (pixel > 15) pixel = 15;

            if (pixel != BG_LEVEL)
                Paint_SetPixel(px, py, (UWORD)pixel);
        }
    }

    // --- Pass 2: blit pre-rendered text sprites ---
    for (int i = 0; i < NUM_SEGMENTS; i++) {
        float theta_from_top = i * SEGMENT_ANGLE + rotation;
        while (theta_from_top < -180.0f) theta_from_top += 360.0f;
        while (theta_from_top >  180.0f) theta_from_top -= 360.0f;
        if (theta_from_top < -32.0f || theta_from_top > 32.0f) continue;

        int ai = angle_index(theta_from_top);
        const NoteSprite *sp = &note_sprites[i][ai];
        if (sp->w == 0) continue;

        for (int sy = 0; sy < sp->h; sy++) {
            int py = sp->oy + sy;
            if (py < 0 || py >= HEIGHT) continue;
            for (int sx = 0; sx < sp->w; sx++) {
                int px = sp->ox + sx;
                if (px < 0 || px >= WIDTH) continue;

                uint8_t text_alpha = sprite_get(sp->pixels, sx, sy, sp->w);
                if (text_alpha == 0) continue;

                /* Segment (hence fill grey) under this pixel, from the LUT. */
                uint8_t hi = s_lut[(py * WIDTH + px) * 2] >> 4;
                uint8_t bg = BG_LEVEL;
                if (hi < NUM_SEGMENTS) {
                    int seg = hi + rot_steps;
                    if (seg >= NUM_SEGMENTS) seg -= NUM_SEGMENTS;
                    bg = seg_grey[seg];
                }

                int pixel = (bg * (15 - text_alpha) + 7) / 15;
                if (pixel > 15) pixel = 15;

                Paint_SetPixel(px, py, (UWORD)pixel);
            }
        }
    }

}
